cillian64/bigtime/firmware/sntp.c

#include <string.h>
#include <lwip/sockets.h>
#include <lwip/netdb.h>
#include <stdint.h>
#include "sntp.h"

// Danger Will Robinson!
// htobe64 and be64toh don't exist everywhere.
#define IS_BIG_ENDIAN (*(uint16_t *)"\0\xff" < 0x100)
uint64_t hton64(uint64_t in)
{
    uint64_t out = 0;
    if(IS_BIG_ENDIAN)
        return in;
    out |= (uint64_t)htonl(in & 0xffffffff) << 32;
    out |= htonl(in >> 32);
    return out;
}
uint64_t ntoh64(uint64_t in)
{
    uint64_t out = 0;
    if(IS_BIG_ENDIAN)
        return in;
    out |= (uint64_t)htonl(in & 0xffffffff) << 32;
    out |= htonl(in >> 32);
    return out;
}

const int dst_ntp_port = 123;
const int src_ntp_port = 123;

#define NTP_FLAG_LEAP_MASK      0xc0 // 0b11000000
#define NTP_FLAG_LEAP_SHIFT     6
#define NTP_FLAG_VERSION_MASK   0x38 // 0b00111000
#define NTP_FLAG_VERSION_SHIFT  3
#define NTP_FLAG_MODE_MASK      0x07 // 0b00000111
#define NTP_FLAG_MODE_SHIFT     0

struct ntp_packet {
    uint8_t flags;
    uint8_t stratum;
    uint8_t poll_interval;
    uint8_t precision;

    // Word-aligned fields
    uint32_t root_delay;
    uint32_t root_dispersion;
    uint32_t reference_id;
    uint64_t reference_timestamp;
    uint64_t origin_timestamp;
    uint64_t receive_timestamp;
    uint64_t transmit_timestamp;
};

// Convert NTP packet from host to network endian-ness
void hton_ntp(struct ntp_packet *packet)
{
    packet->root_delay = htonl(packet->root_delay);
    packet->root_dispersion = htonl(packet->root_dispersion);
    packet->reference_id = htonl(packet->reference_id);
    packet->reference_timestamp = hton64(packet->reference_timestamp);
    packet->origin_timestamp = hton64(packet->origin_timestamp);
    packet->receive_timestamp = hton64(packet->receive_timestamp);
    packet->transmit_timestamp = hton64(packet->transmit_timestamp);
}

// Convert NTP packet from network to host endian-ness
void ntoh_ntp(struct ntp_packet *packet)
{
    packet->root_delay = ntohl(packet->root_delay);
    packet->root_dispersion = ntohl(packet->root_dispersion);
    packet->reference_id = ntohl(packet->reference_id);
    packet->reference_timestamp = ntoh64(packet->reference_timestamp);
    packet->origin_timestamp = ntoh64(packet->origin_timestamp);
    packet->receive_timestamp = ntoh64(packet->receive_timestamp);
    packet->transmit_timestamp = ntoh64(packet->transmit_timestamp);
}

// Send the packet `tx' to the NTP server, then receive packet `rx'
// Returns SNTP_SUCCESS or SNTP_NOREPLY in case of a network error
int ntp_exchange(const char* host, int port, struct ntp_packet *tx,
                  struct ntp_packet *rx)
{
    int sockfd, result;
    struct sockaddr_in dst_addr, src_addr;
    struct hostent *resolv;
    socklen_t dst_len;

    // Open the socket
    sockfd = socket(AF_INET, SOCK_DGRAM, 0);
    if (sockfd < 0)
        return SNTP_NETWORK;

    // Resolve the server hostname
    resolv = gethostbyname(host);
    if (resolv == NULL)
    {
        close(sockfd);
        return SNTP_NETWORK;
    }

    // Build the destination address
    memset(&dst_addr, 0, sizeof(dst_addr));
    dst_addr.sin_family = AF_INET;
    memcpy(&dst_addr.sin_addr.s_addr, resolv->h_addr, resolv->h_length);
    dst_addr.sin_port = htons(port);

    // Build the source adddress
    memset(&src_addr, 0, sizeof(src_addr));
    src_addr.sin_family = AF_INET;
    src_addr.sin_addr.s_addr = htonl(INADDR_ANY);
    src_addr.sin_port = htons(src_ntp_port);

    // Packet to network endian-ness
    hton_ntp(tx);

    // Bind to socket
    if(bind(sockfd, (struct sockaddr*)&src_addr, sizeof(src_addr)) < 0)
    {
        close(sockfd);
        return SNTP_NETWORK;
    }

    // Send the message to the server
    result = sendto(sockfd, tx, sizeof(struct ntp_packet), 0,
                    (struct sockaddr *)&dst_addr, sizeof(dst_addr));
    if (result < 0)
    {
        close(sockfd);
        return SNTP_NETWORK;
    }

    // Blocking receive with timeout
    struct timeval timeout;
    timeout.tv_sec = 1;
    timeout.tv_usec = 0;
    fd_set read_fds;
    FD_ZERO(&read_fds);
    FD_SET(sockfd, &read_fds);
    int ret = lwip_select(sockfd+1, &read_fds, NULL, NULL, &timeout);
    if(ret < 0)
        chSysHalt("Error from lwip_select");
    else if(ret == 0)
    {
        close(sockfd);
        return SNTP_NETWORK;
    }

    dst_len = (socklen_t)sizeof(dst_addr);
    result = recvfrom(sockfd, rx, sizeof(struct ntp_packet), 0,
                      (struct sockaddr *)&dst_addr,
                      &dst_len);

    // Packet to machine endian-ness
    ntoh_ntp(rx);

    close(sockfd);
    if (result < 0)
        return SNTP_NETWORK;
    return SNTP_SUCCESS;
}

int get_ntp_timestamp(char *ntp_host, uint64_t *timestamp)
{
    struct ntp_packet tx, rx;

    memset(&tx, 0, sizeof(tx));
    memset(&rx, 0, sizeof(rx));

    tx.flags |= 3 << NTP_FLAG_LEAP_SHIFT;       // Unsynchronised
    tx.flags |= 4 << NTP_FLAG_VERSION_SHIFT;    // NTPv4/SNTPv4
    tx.flags |= 3 << NTP_FLAG_MODE_SHIFT;       // Client
    tx.stratum = 16;                            // Unsynchronised
    tx.poll_interval = 12;                      // 2^10 second poll interval
    tx.precision = 0;                           // 2^(-0)s clock precision

    // Set all timestamps to a reasonable baseline
    tx.origin_timestamp = (uint64_t)(86400U * (365U * 70U + 17U)) << 32;
    tx.reference_timestamp = (uint64_t)(86400U * (365U * 70U + 17U)) << 32;
    tx.receive_timestamp = (uint64_t)(86400U * (365U * 70U + 17U)) << 32;
    tx.transmit_timestamp = (uint64_t)(86400U * (365U * 70U + 17U)) << 32;

    if(ntp_exchange(ntp_host, dst_ntp_port, &tx, &rx) != SNTP_SUCCESS)
        return SNTP_NETWORK;

    // Detect kiss-of-death packets
    if(rx.stratum == 0)
    {
        char *kod = (char*)&rx.reference_id;
        if((memcmp(kod, "DENY", 4) == 0) ||
           (memcmp(kod, "RSTR", 4) == 0))
            return SNTP_KOD_DENY;
        if(memcmp(kod, "RATE", 4) == 0)
            return SNTP_KOD_RATE;
        return SNTP_KOD_OTHER;
    }

    *timestamp = rx.transmit_timestamp;
    return SNTP_SUCCESS;
}
